ayourk/Nabu-PC/Docs/mis-l-13-57.pdf

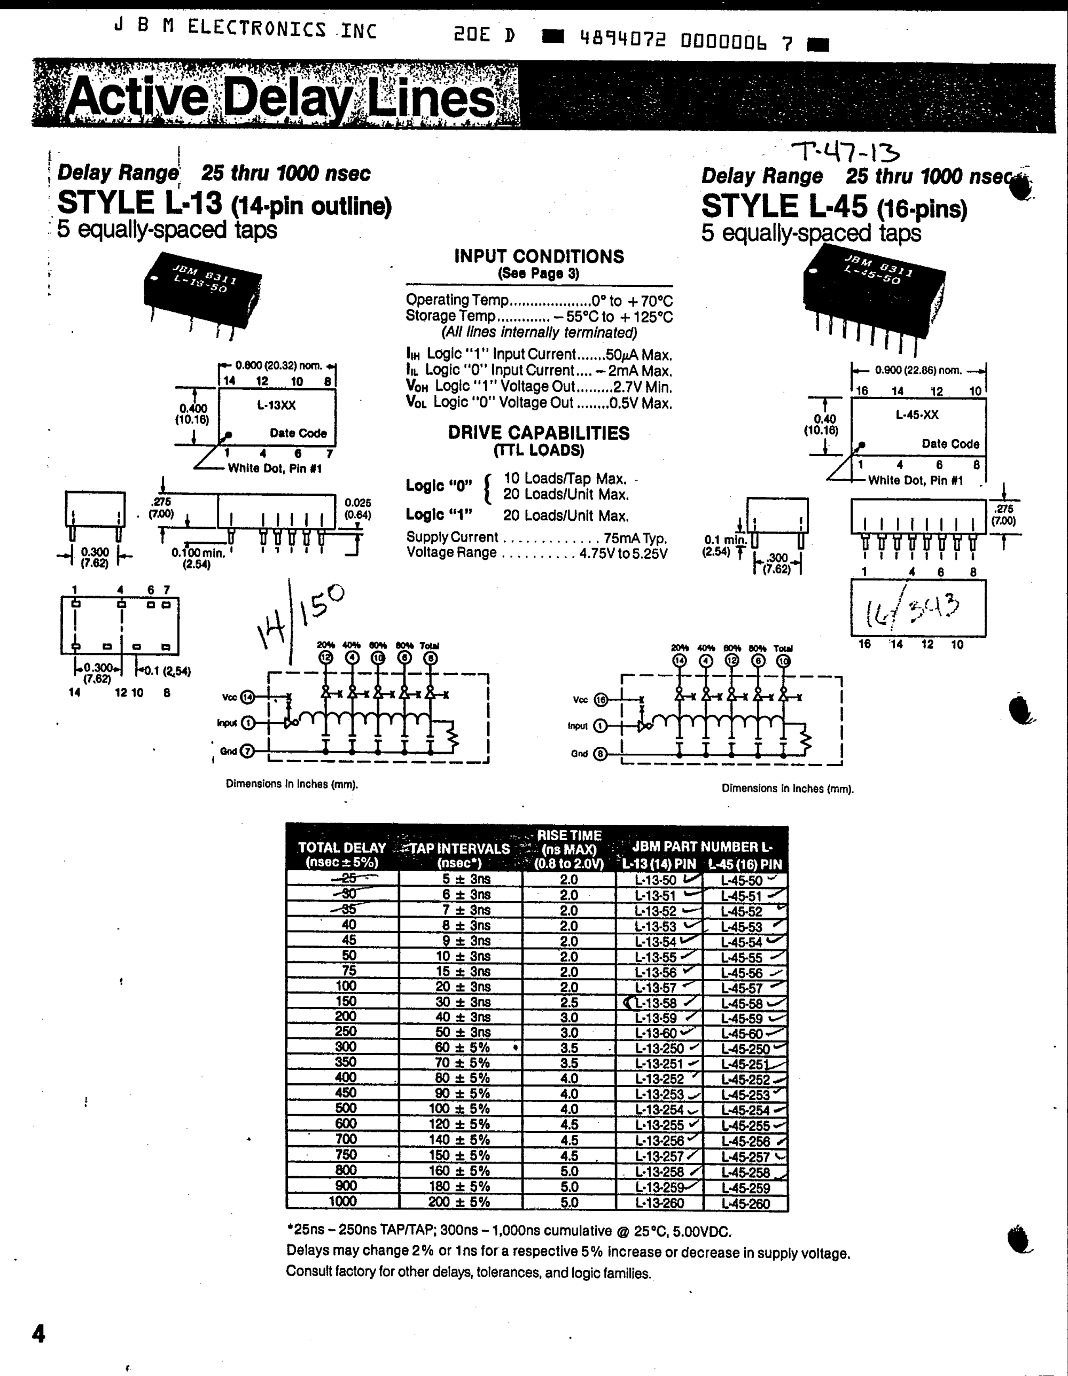
[picture p124: page 1]
