ayourk/Nabu-PC/Nabu-PC.kicad_pcb

## KiCad design sch/Z80proto1(suspend)/Z80proto1.kicad_sch

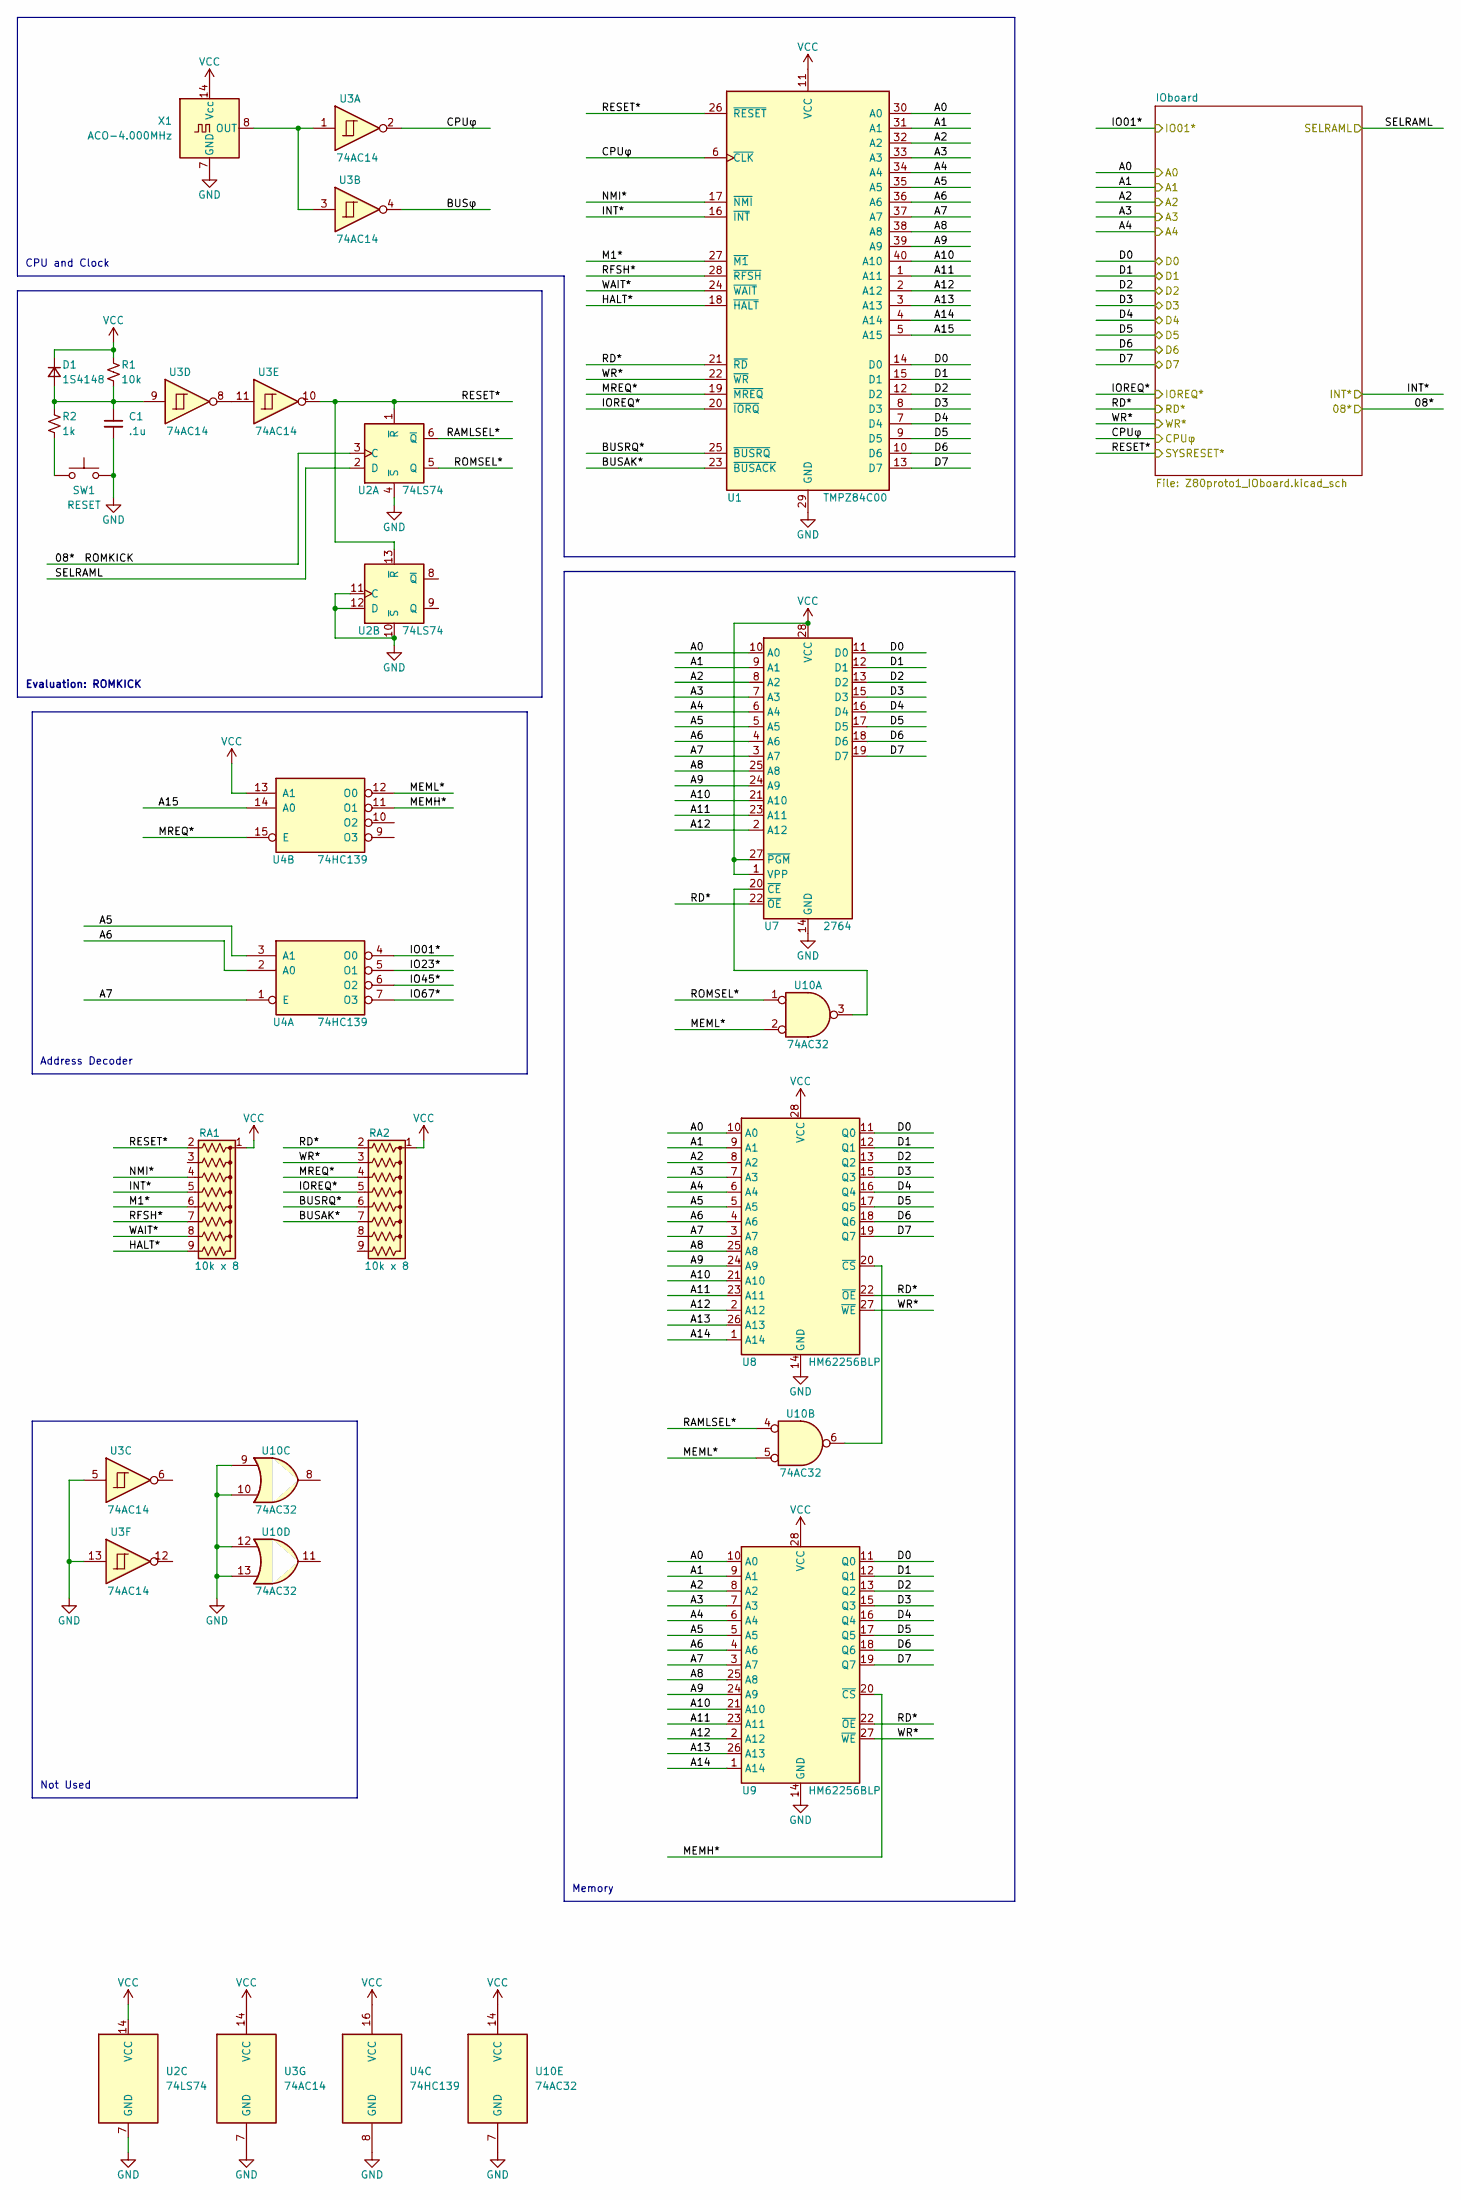
[picture p142: schematic Z80proto1.kicad_sch]

Parts:
C1: .1u
D1: 1S4148
R1: 10k
R2: 1k
RA1, RA2: 10k x 8; R_Array_SIP9
SW1: RESET
U1: TMPZ84C00
U2: 74LS74
U3: 74AC14
U4: 74HC139
U7: 2764; DIP-28_W15.24mm
U8, U9: HM62256BLP; DIP-28_W15.24mm
U10: 74AC32
X1: ACO-4.000MHz; Oscillator_DIP-14

Connections:
08*: U2.3 (C)
A0: U1.30 (A0), U7.10 (A0), U8.10 (A0), U9.10 (A0)
A1: U1.31 (A1), U7.9 (A1), U8.9 (A1), U9.9 (A1)
A2: U1.32 (A2), U7.8 (A2), U8.8 (A2), U9.8 (A2)
A3: U1.33 (A3), U7.7 (A3), U8.7 (A3), U9.7 (A3)
A4: U1.34 (A4), U7.6 (A4), U8.6 (A4), U9.6 (A4)
A5: U1.35 (A5), U4.3 (A1), U7.5 (A5), U8.5 (A5), U9.5 (A5)
A6: U1.36 (A6), U4.2 (A0), U7.4 (A6), U8.4 (A6), U9.4 (A6)
A7: U1.37 (A7), U4.1 (E), U7.3 (A7), U8.3 (A7), U9.3 (A7)
A8: U1.38 (A8), U7.25 (A8), U8.25 (A8), U9.25 (A8)
A9: U1.39 (A9), U7.24 (A9), U8.24 (A9), U9.24 (A9)
A10: U1.40 (A10), U7.21 (A10), U8.21 (A10), U9.21 (A10)
A11: U1.1 (A11), U7.23 (A11), U8.23 (A11), U9.23 (A11)
A12: U1.2 (A12), U7.2 (A12), U8.2 (A12), U9.2 (A12)
A13: U1.3 (A13), U8.26 (A13), U9.26 (A13)
A14: U1.4 (A14), U8.1 (A14), U9.1 (A14)
A15: U1.5 (A15), U4.14 (A0)
BUSAK*: RA2.7 (R6), U1.23 (~BUSACK)
BUSRQ*: RA2.6 (R5), U1.25 (~BUSRQ)
BUSφ: U3.4
CPUφ: U1.6 (~CLK), U3.2
D0: U1.14 (D0), U7.11 (D0), U8.11 (Q0), U9.11 (Q0)
D1: U1.15 (D1), U7.12 (D1), U8.12 (Q1), U9.12 (Q1)
D2: U1.12 (D2), U7.13 (D2), U8.13 (Q2), U9.13 (Q2)
D3: U1.8 (D3), U7.15 (D3), U8.15 (Q3), U9.15 (Q3)
D4: U1.7 (D4), U7.16 (D4), U8.16 (Q4), U9.16 (Q4)
D5: U1.9 (D5), U7.17 (D5), U8.17 (Q5), U9.17 (Q5)
D6: U1.10 (D6), U7.18 (D6), U8.18 (Q6), U9.18 (Q6)
D7: U1.13 (D7), U7.19 (D7), U8.19 (Q7), U9.19 (Q7)
HALT*: RA1.9 (R8), U1.18 (~HALT)
INT*: RA1.5 (R4), U1.16 (~INT)
IO01*: U4.4 (O0)
IO23*: U4.5 (O1)
IO45*: U4.6 (O2)
IO67*: U4.7 (O3)
IOREQ*: RA2.5 (R4), U1.20 (~IORQ)
M1*: RA1.6 (R5), U1.27 (~M1)
MEMH*: U4.11 (O1), U9.20 (~CS)
MEML*: U4.12 (O0), U10.2, U10.5
MREQ*: RA2.4 (R3), U1.19 (~MREQ), U4.15 (E)
NMI*: RA1.4 (R3), U1.17 (~NMI)
unnamed: C1.1, D1.2 (A), R1.2, R2.1, U3.9
unnamed: C1.2, SW1.2
unnamed: D1.1 (K), R1.1
unnamed: R2.2, SW1.1
unnamed: U2.10 (~S), U2.11 (C), U2.12 (D)
unnamed: U3.1, U3.3, X1.8 (OUT)
unnamed: U3.8, U3.11
unnamed: U3.5, U3.13
unnamed: U7.1 (VPP), U7.27 (~PGM), U7.28 (VCC)
unnamed: U7.20 (~CE), U10.3
unnamed: U8.20 (~CS), U10.6
unnamed: U10.9, U10.10, U10.12, U10.13
RAMLSEL*: U2.6 (~Q), U10.4
RD*: RA2.2 (R1), U1.21 (~RD), U7.22 (~OE), U8.22 (~OE), U9.22 (~OE)
RESET*: RA1.2 (R1), U1.26 (~RESET), U2.1 (~R), U2.13 (~R), U3.10
RFSH*: RA1.7 (R6), U1.28 (~RFSH)
ROMSEL*: U2.5 (Q), U10.1
SELRAML: U2.2 (D)
WAIT*: RA1.8 (R7), U1.24 (~WAIT)
WR*: RA2.3 (R2), U1.22 (~WR), U8.27 (~WE), U9.27 (~WE)

Notes on the sheet:
Evaluation: ROMKICK
Memory
CPU and Clock
Address Decoder
Not Used
