ayourk/Nabu-PC/Nabu-PC.kicad_pcb

## KiCad design sch/Z80proto2/Z80proto2_IOblock.kicad_sch

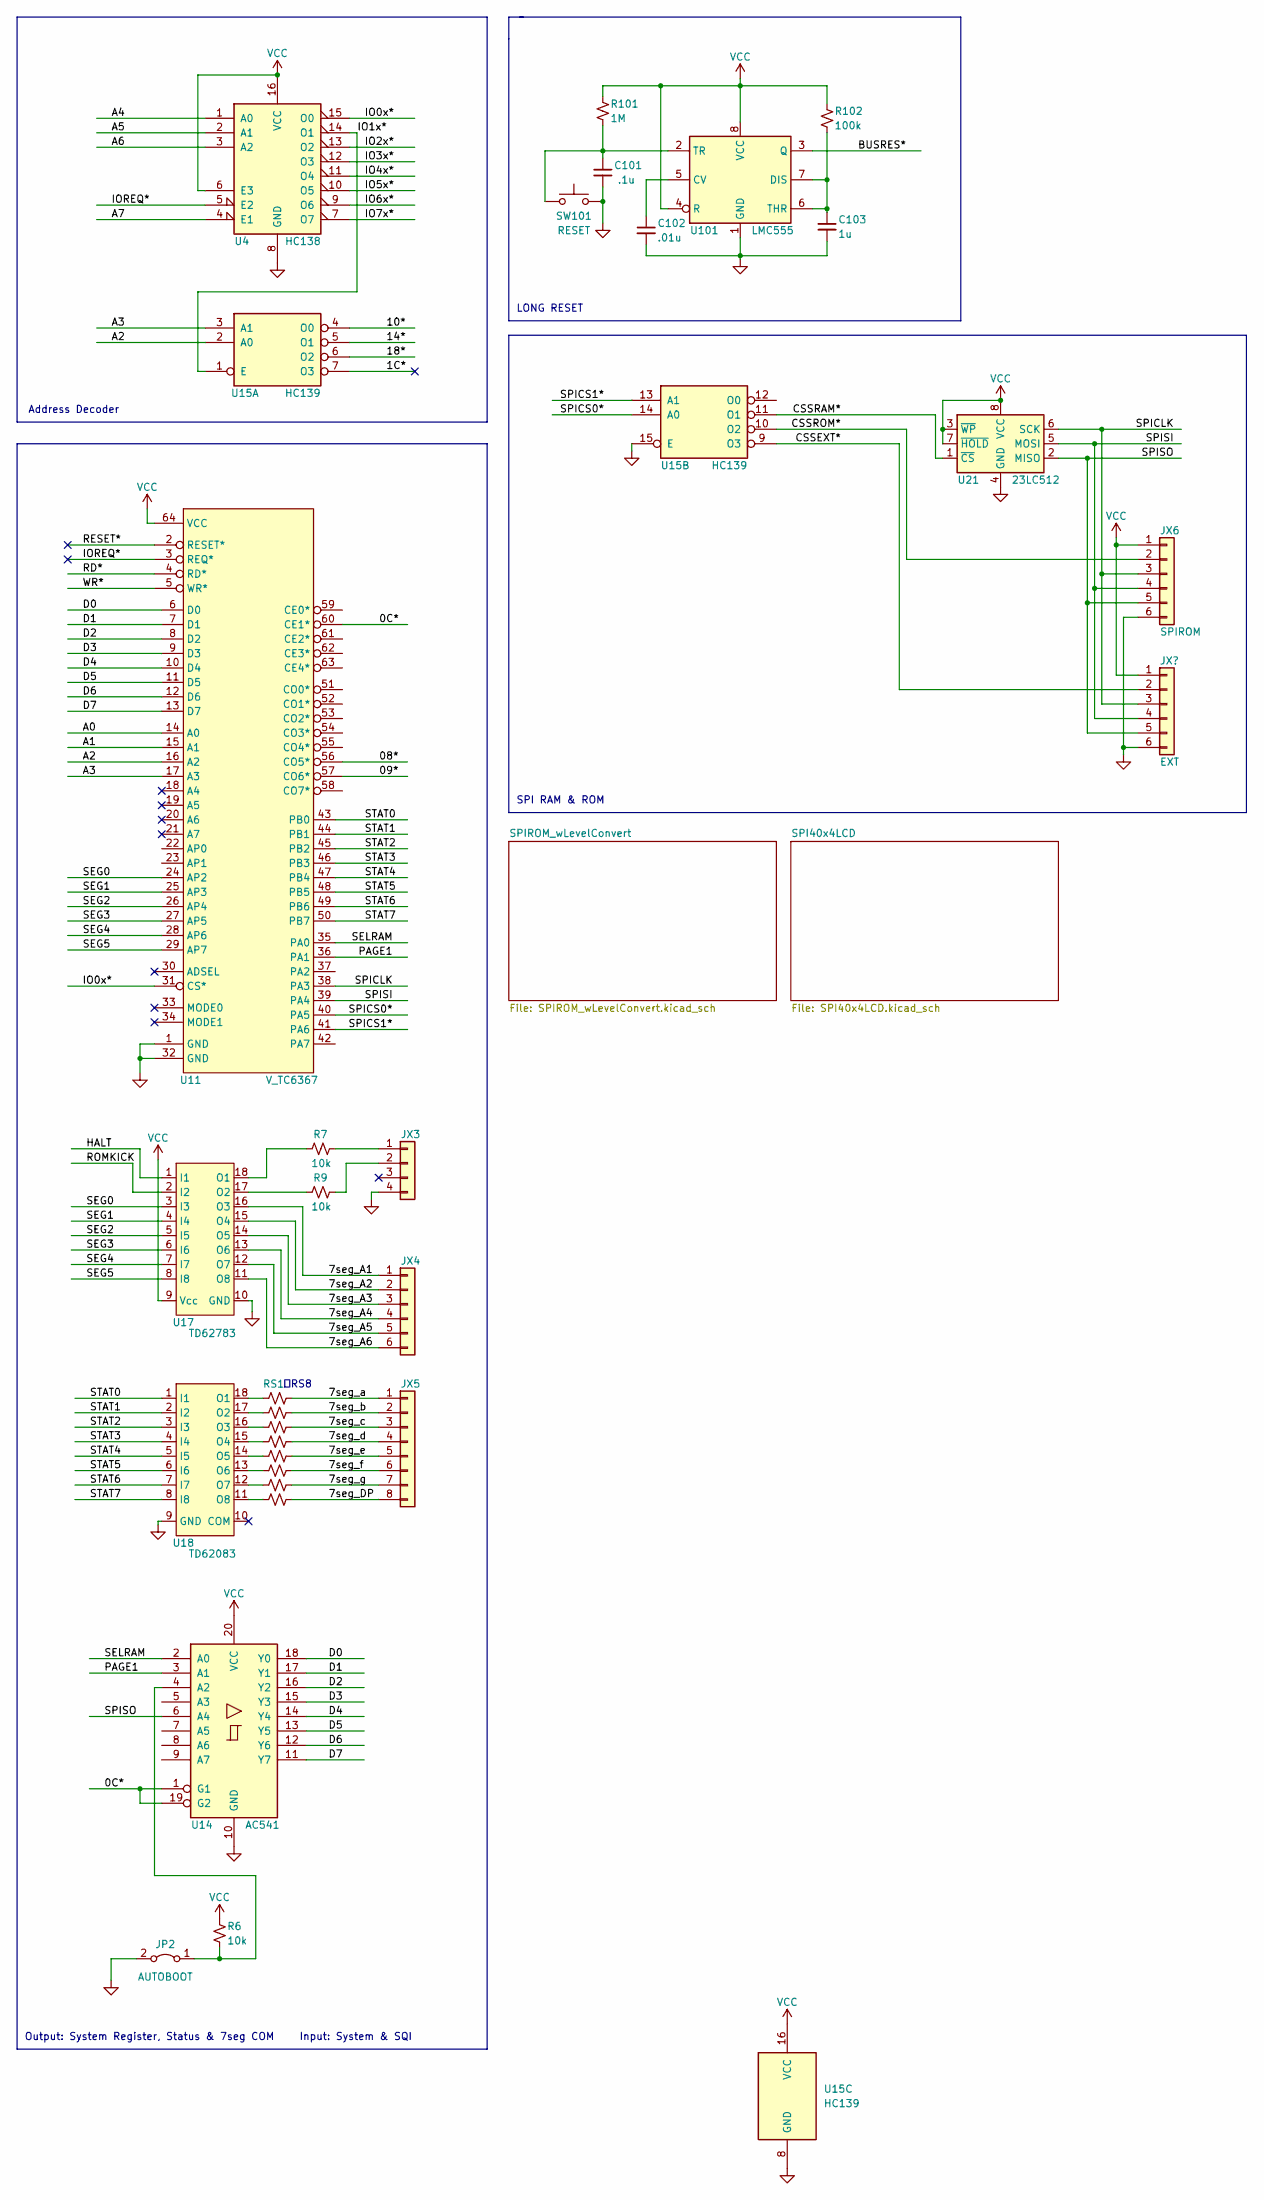
[picture p150: schematic Z80proto2_IOblock.kicad_sch]

Parts:
C101: .1u
C102: .01u
C103: 1u
JP2: AUTOBOOT
JX3: Conn_01x04
JX4: Conn_01x06
JX5: Conn_01x08
JX6: SPIROM
R6, R7, R9: 10k
R101: 1M
R102: 100k
RS1, RS2, RS3, RS4, RS5, RS6, RS7, RS8: 1k
SW101: RESET
U4: HC138
U11: V_TC6367
U14: AC541
U15: HC139
U17: TD62783
U18: TD62083
U21: 23LC512
U101: LMC555; DIP-8_W7.62mm

Connections:
0C*: U11.60 (CE1*), U14.1 (G1), U14.19 (G2)
1C*: U15.7 (O3)
7seg_A1: JX4.1, U17.16 (O3)
7seg_A2: JX4.2, U17.15 (O4)
7seg_A3: JX4.3, U17.14 (O5)
7seg_A4: JX4.4, U17.13 (O6)
7seg_A5: JX4.5, U17.12 (O7)
7seg_A6: JX4.6, U17.11 (O8)
7seg_DP: JX5.8, RS8.2
7seg_a: JX5.1, RS1.2
7seg_b: JX5.2, RS2.2
7seg_c: JX5.3, RS3.2
7seg_d: JX5.4, RS4.2
7seg_e: JX5.5, RS5.2
7seg_f: JX5.6, RS6.2
7seg_g: JX5.7, RS7.2
08*: U11.56 (CO5*)
09*: U11.57 (CO6*)
10*: U15.4 (O0)
14*: U15.5 (O1)
18*: U15.6 (O2)
A0: U11.14 (A0)
A1: U11.15 (A1)
A2: U11.16 (A2), U15.2 (A0)
A3: U11.17 (A3), U15.3 (A1)
A4: U4.1 (A0)
A5: U4.2 (A1)
A6: U4.3 (A2)
A7: U4.4 (E1)
BUSRES*: U101.3 (Q)
CSSEXT*: U15.9 (O3)
CSSRAM*: U15.11 (O1), U21.1 (~CS)
CSSROM*: JX6.2, U15.10 (O2)
D0: U11.6 (D0), U14.18 (Y0)
D1: U11.7 (D1), U14.17 (Y1)
D2: U11.8 (D2), U14.16 (Y2)
D3: U11.9 (D3), U14.15 (Y3)
D4: U11.10 (D4), U14.14 (Y4)
D5: U11.11 (D5), U14.13 (Y5)
D6: U11.12 (D6), U14.12 (Y6)
D7: U11.13 (D7), U14.11 (Y7)
HALT: U17.1 (I1)
IO0x*: U4.15 (O0), U11.31 (CS*)
IO1x*: U4.14 (O1), U15.1 (E)
IO2x*: U4.13 (O2)
IO3x*: U4.12 (O3)
IO4x*: U4.11 (O4)
IO5x*: U4.10 (O5)
IO6x*: U4.9 (O6)
IO7x*: U4.7 (O7)
IOREQ*: U4.5 (E2), U11.3 (REQ*)
unnamed: C101.1, R101.2, SW101.1, U101.2 (TR)
unnamed: C101.2, SW101.2
unnamed: C102.1, U101.5 (CV)
unnamed: C102.2, C103.2, U101.1 (GND)
unnamed: C103.1, R102.2, U101.6 (THR), U101.7 (DIS)
unnamed: JP2.1 (A), R6.2, U14.4 (A2)
unnamed: JX3.1, R7.2
unnamed: JX3.2, R9.2
unnamed: R7.1, U17.18 (O1)
unnamed: R9.1, U17.17 (O2)
unnamed: R101.1, R102.1, U101.4 (R), U101.8 (VCC)
unnamed: RS1.1, U18.18 (O1)
unnamed: RS2.1, U18.17 (O2)
unnamed: RS3.1, U18.16 (O3)
unnamed: RS4.1, U18.15 (O4)
unnamed: RS5.1, U18.14 (O5)
unnamed: RS6.1, U18.13 (O6)
unnamed: RS7.1, U18.12 (O7)
unnamed: RS8.1, U18.11 (O8)
unnamed: U4.6 (E3), U4.16 (VCC)
unnamed: U11.1 (GND), U11.32 (GND)
unnamed: U21.3 (~WP), U21.7 (~HOLD), U21.8 (VCC)
PAGE1: U11.36 (PA1), U14.3 (A1)
RD*: U11.4 (RD*)
RESET*: U11.2 (RESET*)
ROMKICK: U17.2 (I2)
SEG0: U11.24 (AP2), U17.3 (I3)
SEG1: U11.25 (AP3), U17.4 (I4)
SEG2: U11.26 (AP4), U17.5 (I5)
SEG3: U11.27 (AP5), U17.6 (I6)
SEG4: U11.28 (AP6), U17.7 (I7)
SEG5: U11.29 (AP7), U17.8 (I8)
SELRAM: U11.35 (PA0), U14.2 (A0)
SPICLK: JX6.3, U11.38 (PA3), U21.6 (SCK)
SPICS0*: U11.40 (PA5), U15.14 (A0)
SPICS1*: U11.41 (PA6), U15.13 (A1)
SPISI: JX6.4, U11.39 (PA4), U21.5 (MOSI)
SPISO: JX6.5, U14.6 (A4), U21.2 (MISO)
STAT0: U11.43 (PB0), U18.1 (I1)
STAT1: U11.44 (PB1), U18.2 (I2)
STAT2: U11.45 (PB2), U18.3 (I3)
STAT3: U11.46 (PB3), U18.4 (I4)
STAT4: U11.47 (PB4), U18.5 (I5)
STAT5: U11.48 (PB5), U18.6 (I6)
STAT6: U11.49 (PB6), U18.7 (I7)
STAT7: U11.50 (PB7), U18.8 (I8)
WR*: U11.5 (WR*)

Notes on the sheet:
SPI RAM & ROM
Output: System Register, Status & 7seg COM
LONG RESET
Input: System & SQI
～RS8
Address Decoder
